G-Wiley/RK05_Emulator_Tester_System_v2/Setting up the emulator.pdf

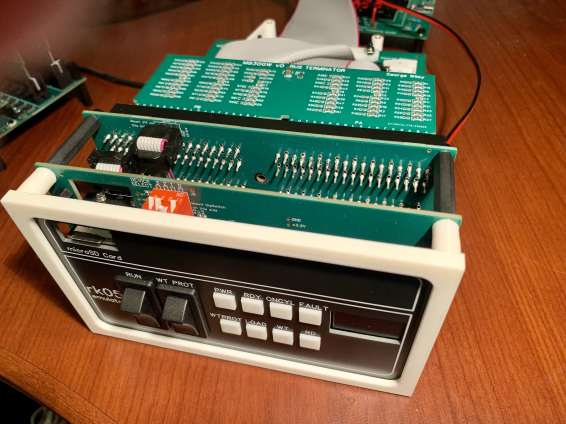
[picture p1: figure]

14-May-2026 | Seng up the emulator v09.docx | Page 1

Connecng the emulator to the Disk Controller:
- The order of the following setup steps isn’t important except to turn the power on as the last step.
- Plug in the terminator board and the “A1” or “A2” RK05 bus interface cable. The two RK05 bus slots on the emulator are electrically the same so either board can go in either slot. The component side faces up. It’s easier to access the Adapter Board when the terminator board is installed in the top slot. It might also be convenient to connect oscilloscope probes to the RK05 bus signals from the top of the M993GW adapter board, and in that case it’s beer to plug the terminator into the boom connector.

There is a keying slot between the two sets of gold contact fingers on both the terminator board and on the cable. There is a guide on the emulator main board silkscreen that shows the proper orientaon of this keying slot.

Silkscreen guide, corresponds to the keying slot

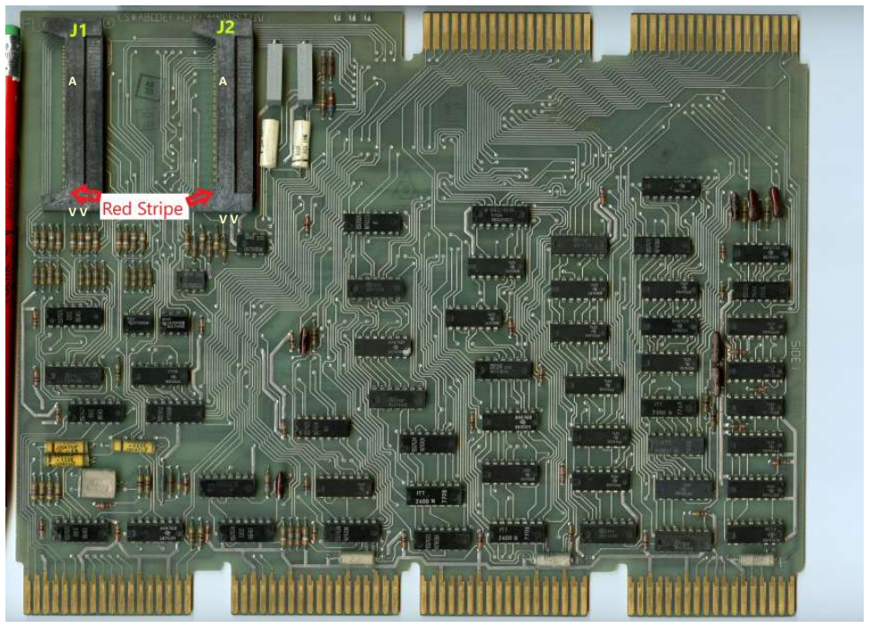
[picture p2: figure]

14-May-2026 | Seng up the emulator v09.docx | Page 2

Connecng to a Disk Controller, PDP-8 Systems
- DEC RK8-E: Connect the unconnected ends of the flat cables from an “A1” RK05-to-RK8-E Cable to the DEC RK8-E M7106 connectors J1 & J2. Connect the flat cable from J1 on the M993GW Adapter Board to J1 on the M7106. Similarly, connect the flat cable from J2 on the M993GW adapter card to J2 on the M7106. It is helpful to use a permanent marker or other means to label the flat cables with “J1” & “J2” so it is clear which cable goes to which connector. If connecng to a DEC RK8-E, then the keying tabs on the flat cable connectors should be sanded off so they will fit into the DEC Berg connectors. A Dremel tool or sharp pair of flush cut diagonal cuers (or both) can also be used to remove the keying tabs. The pin numbering alignment is strange, as shown in the photo: 3M connector pin 1 (red stripe) corresponds to Berg pin VV, and 3M pin 40 corresponds to Berg pin A.

DEC RK8-E

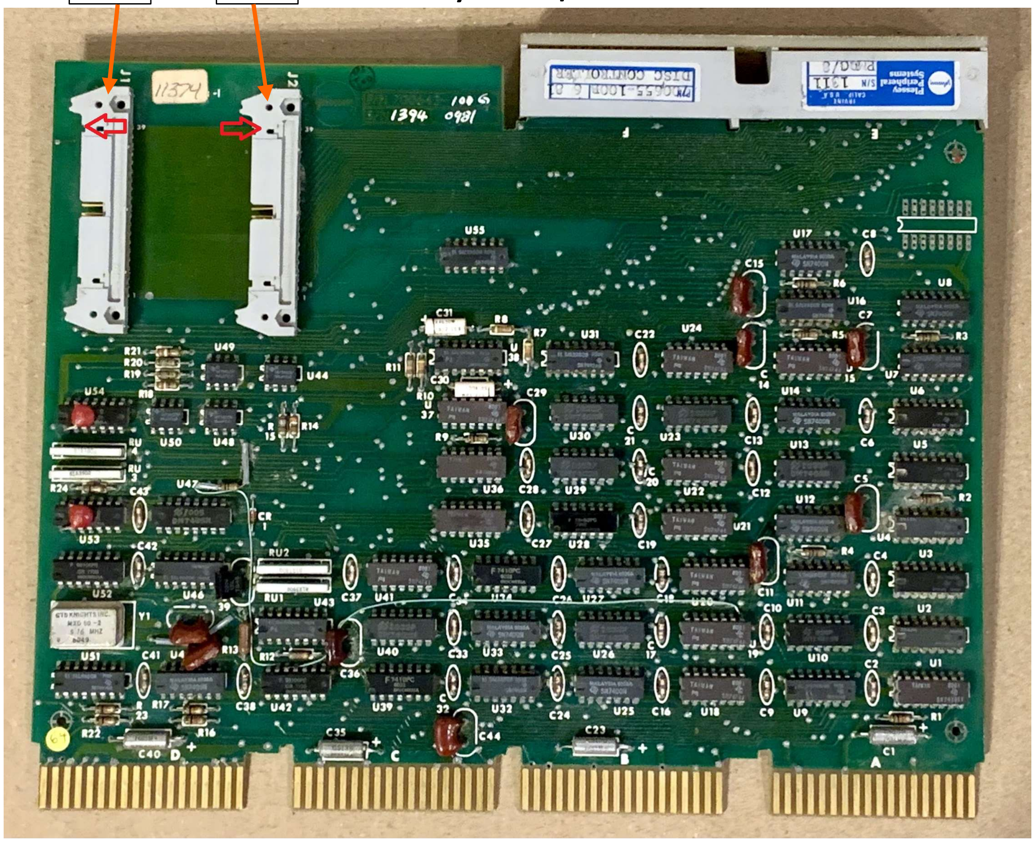
[picture p3: figure]

14-May-2026 | Seng up the emulator v09.docx | Page 3
- The Plessey PM-DC/8 has J1 & J2 clearly labelled on the silkscreen. J1 on the M993GW (emulator accessory A1 or A4) connects to J1 on the PM-DC/8, and J2 on the M993GW connects to J2 on the PM-DC/8. Red arrows in the photo below show the orientaon of the red stripe on the cable. Note that this is the opposite orientaon compared to the DEC RK8-E. The keying slots on the controller board headers are not in the proper orientaon to accept the keying ribs on the cables from the emulator.

The keying tabs on the flat cable connectors should be sanded off so they will fit into the J1 & J2 connectors on the PM-DC/8. If the keying tab is not removed then the flat cable will only fit into J1 & J2 in the wrong direcon and the red stripe on the cables will be oriented incorrectly (at the boom of J1 & J2). A Dremel tool or sharp pair of flush cut diagonal cuers (or both) can also be used to remove the keying tabs. The pin numbering alignment is strange, as shown in the photo: the red stripe on the cable corresponds to J1 & J2 pins 39 & 40, and the side of the cable without the red stripe corresponds to J1 & J2 pins 1 & 2.

Aer plugging in the cables, ensure that the orientaon of the cables and red stripe are correct.

Plessey PM-DC/8

J1 J2

14-May-2026 | Seng up the emulator v09.docx | Page 4
- OS/8 Bootstrap for RK8-E + RK05
Load the following two-word program, run from 0030:

Address Content
0030 6743
0031 5031

How to:
1. Copy the file “os8.rke” or another suitable OS/8 image to a microSD card.
Confirm that no other rke files exist at the root level on the microSD card.

### 2. Remove the microSD card from your computer and insert the card into the slot on the

front of the RK05 emulator.
3. Flip the RUN/LOAD switch on the front of the RK05 emulator to the “RUN” posion.
4. Wait for the microSD card image to load. When that’s complete, the following lights will be illuminated on the front of the emulator: PWR, RDY, ONCYL
5. Perform the following steps via the front panel of the PDP-8.

### 6. Set SR = 0030 7. ADDR LOAD 8. Set SR = 6743 9. DEP 10. Set SR = 5031 11. DEP 12. Set SR = 0030 13. ADDR LOAD 14. CONT

- Conversion to/from emulator rke files and SIMH RK05 PDP-8 images hps://svn.so-much-stuff.com/svn/trunk/pdp8/8tools/ hps://svn.so-much-stuff.com/svn/trunk/pdp8/8tools/doc/
o dsk2rke converts .dsk format to RKE (emulator) format
PERL: hps://svn.so-much-stuff.com/svn/trunk/pdp8/8tools/dsk2rke
doc: hps://svn.so-much-stuff.com/svn/trunk/pdp8/8tools/doc/dsk2rke.md o rke2dsk converts RKE format to .dsk (SIMH) format
PERL: hps://svn.so-much-stuff.com/svn/trunk/pdp8/8tools/rke2dsk
doc: hps://svn.so-much-stuff.com/svn/trunk/pdp8/8tools/doc/rke2dsk.md o rkechk checks an RKE file and a DSK file for equivalence
PERL: hps://svn.so-much-stuff.com/svn/trunk/pdp8/8tools/rkechk
doc: hps://svn.so-much-stuff.com/svn/trunk/pdp8/8tools/doc/rkechk.md

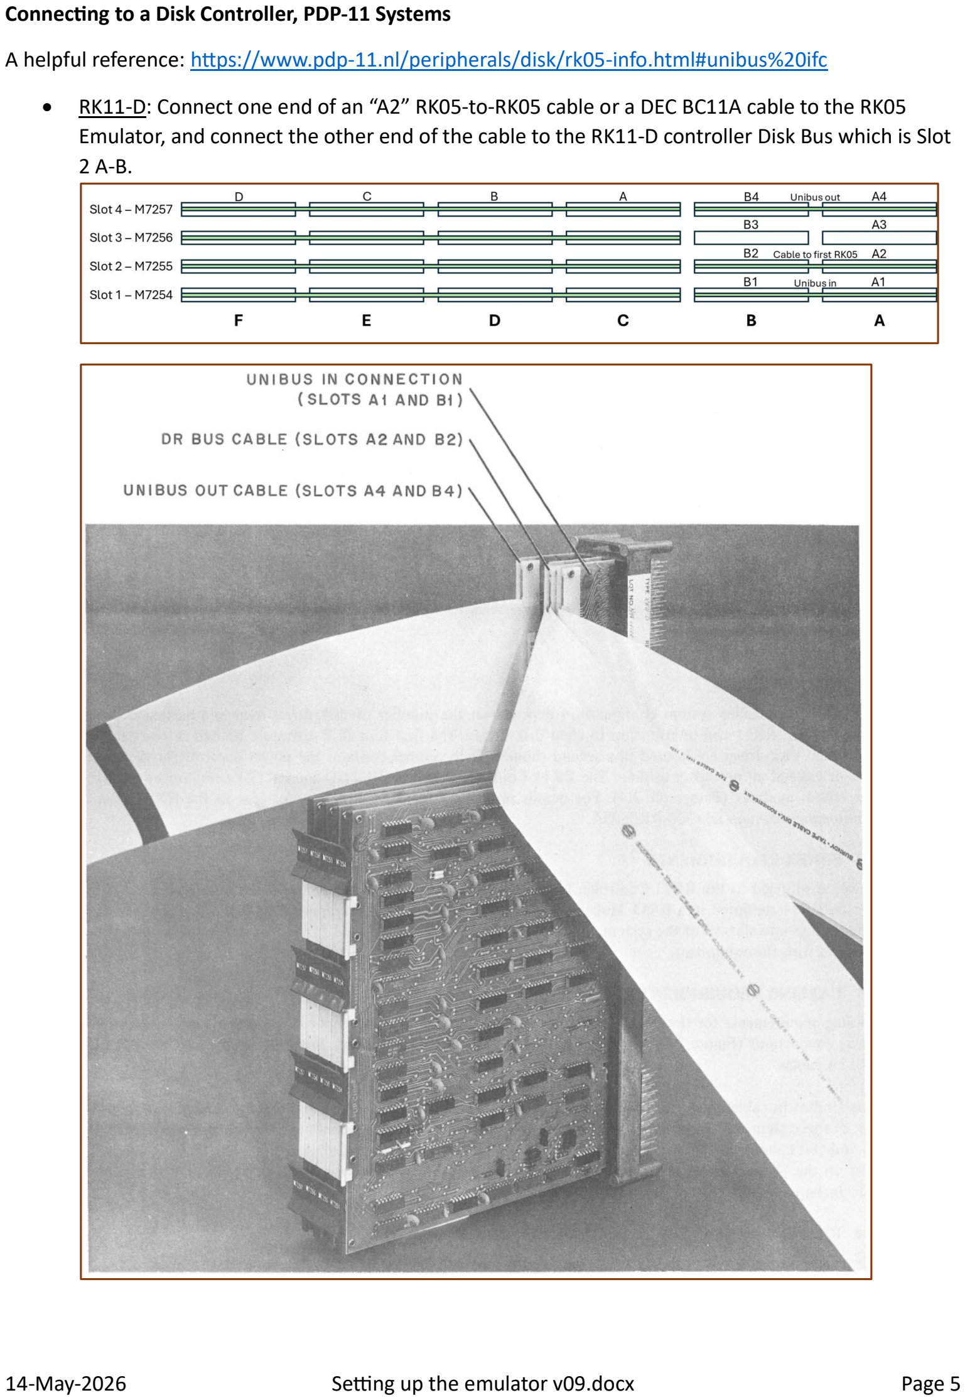
[picture p4: page 5]

14-May-2026 | Seng up the emulator v09.docx | Page 5

Connecng to a Disk Controller, PDP-11 Systems
A helpful reference: hps://www.pdp-11.nl/peripherals/disk/rk05-info.html#unibus%20ifc
- RK11-D: Connect one end of an “A2” RK05-to-RK05 cable or a DEC BC11A cable to the RK05 Emulator, and connect the other end of the cable to the RK11-D controller Disk Bus which is Slot 2 A-B.

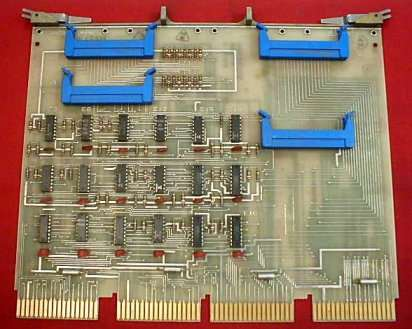
[picture p5: figure]

14-May-2026 | Seng up the emulator v09.docx | Page 6
- RKV11-D: Connect one end of an “A1” RK05-to-RK8-E cable into a slot on the RK05 Emulator. Connect the unconnected ends of the flat cables from the “A1” RK05-to-RK8-E Cable to flat cable connectors on the DEC M7268 board that is part of the RKV11-D controller. It is helpful to use a permanent marker or other means to label the flat cables so it is clear which cable goes to which connector. The keying tabs on the flat cable connectors should be sanded off so they will fit into the DEC Berg connectors. A Dremel tool or sharp pair of flush cut diagonal cuers (or both) can also be used to remove the keying tabs. The pin numbering alignment is strange, as shown in the photo: 3M connector pin 1 (red stripe) corresponds to Berg pin VV, and 3M pin 40 corresponds to Berg pin A.

DEC M7268

Image source: hps://www.pdp-11.nl/peripherals/disk/rk05-info.html#unibus%20ifc

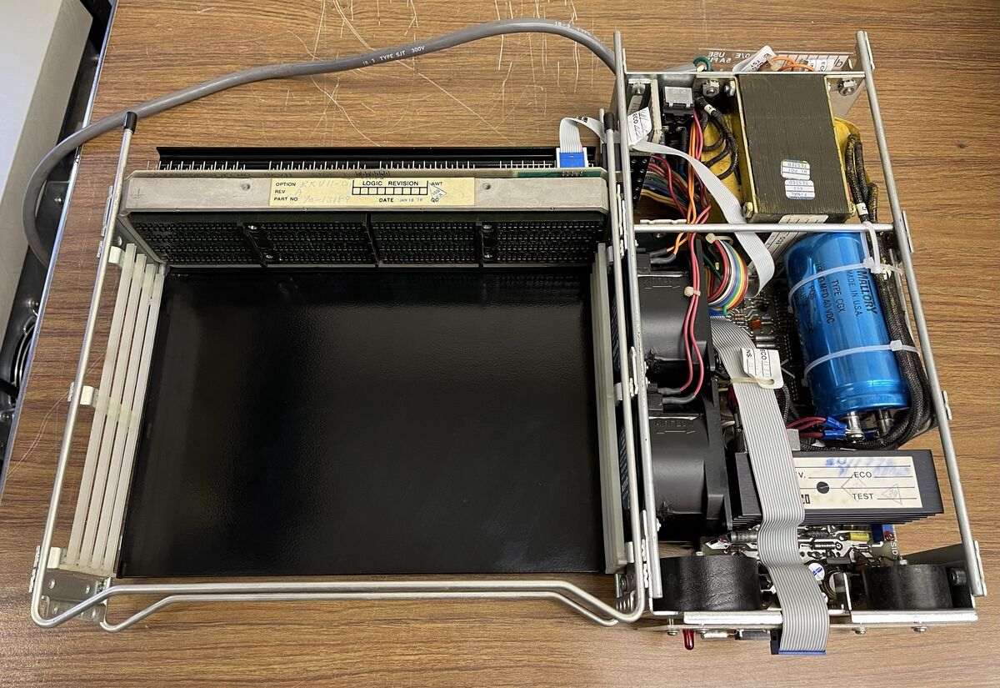
[picture p6: figure]

14-May-2026 | Seng up the emulator v09.docx | Page 7

Image source: hps://gunkies.org/wiki/RK11_disk_controller#RKV11-D

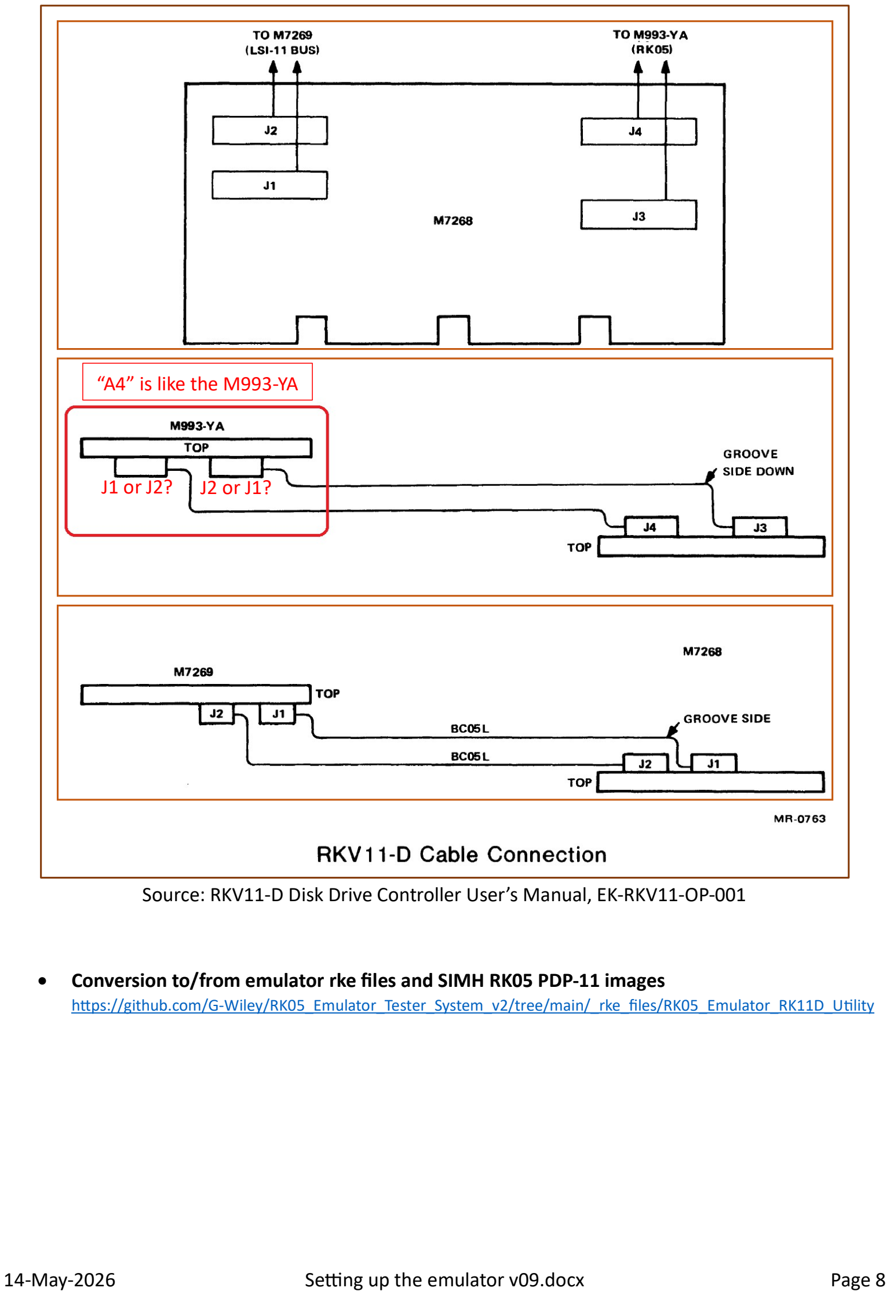
[picture p7: page 8]

14-May-2026 | Seng up the emulator v09.docx | Page 8

Source: RKV11-D Disk Drive Controller User’s Manual, EK-RKV11-OP-001

- Conversion to/from emulator rke files and SIMH RK05 PDP-11 images
hps://github.com/G-Wiley/RK05_Emulator_Tester_System_v2/tree/main/_rke_files/RK05_Emulator_RK11D_Ulity

“A4” is like the M993-YA

J1 or J2? J2 or J1?

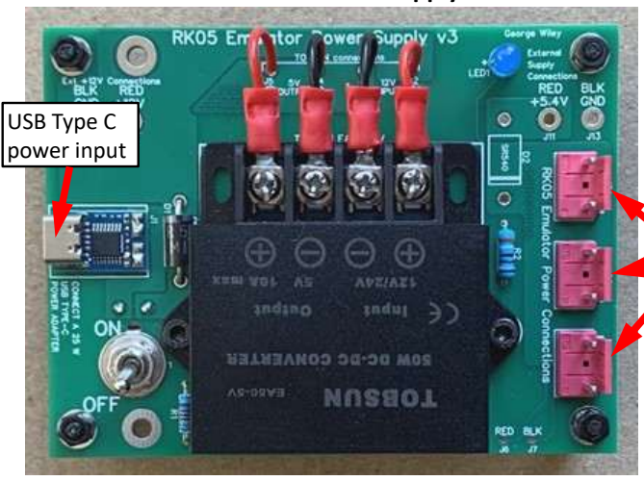
[picture p8: figure]
USB Type C power input

14-May-2026 | Seng up the emulator v09.docx | Page 9

Emulator Power Supply
- Connect one end of the red/black power cable to the power header on the emulator. Connect the other end of the power cable to any one of the three power headers on the Emulator Power Supply. Up to three emulators can be connected to a single Emulator Power Supply.

Emulator Power Supply

- Connect a 25-wa USB Type C power module to the USB Type C connector on the Emulator Power Supply. This Type C power module is included with the “A7” Emulator Power Supply. For example, this is the type of power module shipped with the “A7” kit: hps://www.amazon.com/dp/B097MVXSQ5
Emulator Power Supply versions v2 and above have a power input switch located near the USB connector.

Power
Headers

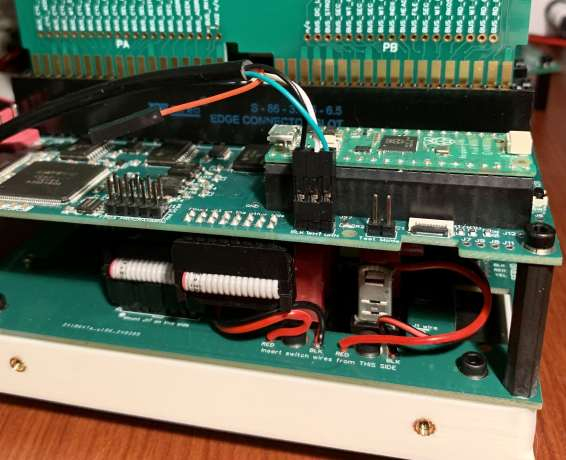
[picture p9: figure]

14-May-2026 | Seng up the emulator v09.docx | Page 10

Connecng a serial console
- If it is necessary to observe the emulator event log data, then connect a USB serial cable to the serial “DEBUG” port, as shown. The black wire is “GND”, white is “TX”, green is “RX”. The red wire on the USB serial cable is unconnected. The silkscreen on the main board indicates which wire color should connect to each of the three pins. Either a 5 volt or 3.3 volt USB serial cable can be used; the emulator has 5 volt tolerant drivers and receivers on the TX and RX signals and is compable with 3.3 volt and 5 volt signal levels. With USB side of the serial cable plugged into in the computer, set your terminal emulator to use whichever COM port is assigned to the cable. Tip: bring up the Windows Device Manager first, then plug the USB cable into the computer to observe which COM port was just assigned when the USB serial cable was inserted. Baud rate is 460,800 bits per second, 8 bits, no parity. The high data rate is used so the serial port can keep up when logging sector reads and writes when the logging mode is selected.
- Set the RUN/LOAD switch on the front panel of the emulator to the “LOAD” posion.
- Plug in the USB Type C charger and turn on the on-board power switch.

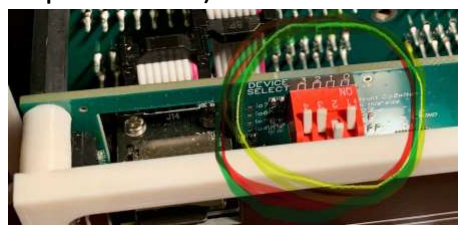
[picture p10: figure]

14-May-2026 | Seng up the emulator v09.docx | Page 11

Using the Emulator:
- Insert a microSD card into the microSD slot accessible through the front panel. The card must have a valid rk05 emulator file with an “rke” file extension at the root level. Example rke files are provided in the emulator repository on github: hps://github.com/G-Wiley/RK05_Emulator_Tester_System_v2/tree/main/_rke_files
The emulator will load the first file it finds that has an rke file extension.
- The Drive Address can be set using the 4-posion dipswitch located behind the front panel. The dipswitch is idenfied as “DEVICE SELECT” on the board silkscreen next to the dipswitch. The individual switches are idenfied as 0 through 3 on the silkscreen. Switches 0 through 2 are a 3-bit binary drive address value. The selected Drive Address immediately appears in the OLED display on the front panel. The Drive Address seng is effecve only when the emulator is in the “LOAD” state.
- The following example shows the switches set to address 2. The switch on the right has binary weight of 2⁰

, the next switch to the le which is in a different state than the other switches is 2¹ ,
the next switch to the le is 2² , and the switch on the far le selects fixed mode (which is not yet implemented).

Although some drives use one-hot individual select enable signals to select the drive, this address switch is always a binary representaon of the drive address. The large digit in the front panel display confirms the address that is selected.
- Aer the RUN/LOAD switch is turned to the RUN posion, the emulator will ignore the state of the dipswitches. Only drive addresses 0 through 3 are valid for PDP-8 RK8-E mode which uses individual select signals on the disk bus. Drive addresses 0-7 can be used in RK11-D/E modes which use a binary-encoded drive address on the disk bus. The disk controller outputs a signal on the disk bus so that drives will use the proper drive-selecon mode for the controller. The RK05 emulator and real RK05 drives respond properly to this signal from the controller, but some other drives (such as Diablo series 30) support only individual select signals. The most significant switch, switch 3, (the switch on the le) enables RK05f mode. RK05f mode is not yet supported; the proper double-address will appear in the display, but the FPGA and soware do not yet support this mode. This is a planned future upgrade.
- Flip the RUN/LOAD switch to the “RUN” posion. The emulator will read the rk05 disk image file from the card and store the data in the emulator’s DRAM. Progress of reading the file will appear in the display. When the enre file has been read, the front panel LEDs will update to indicate RDY and ONCYL.
- To observe a log of RK05 bus events such as Seek, Restore, Read and Write: type “L” on the aached terminal (commands are case insensive). To stop logging type “S”. There is a bug which may cause the emulator to lock up aer receiving 5,000 to 10,000 bus events while logging. This problem does not occur when logging is off.

14-May-2026 | Seng up the emulator v09.docx | Page 12
- To unload and save data from the emulator DRAM back to the microSD card, flip the RUN/LOAD switch back to the LOAD posion. Progress of wring the file will appear in the display. When the enre file has been wrien, the front panel LEDs will update to indicate LOAD.
- If there is an error, then it will show in the emulator front panel display and on the aached terminal and the ERROR indicator on the front panel will flash. The flashing error indicator can be cleared by first holding the WTPROT switch while toggling the state of the RUN/LOAD switch.
