G-Wiley/RK05_Emulator_Tester_System_v2/_rke_files/Sector Timing and Data Diagrams v05.pdf

Bit times from sector pulse to start bit Number of data bits after the start bit Data Block, includes Cylinder Address, data, CRC, etc.

Ideally this is only the data between the Sync Bit and Postamble, but it may contain some of the all-zero Postamble bits

1w 1w | 1 to n 16-bit words
Preamble | S | Cylinder Address, Data, CRC, etc. | Postamble

Disk_Sector_Pulse_L

RK8-E Write_Gate_L

DG Write_Gate_L

Read_Gate_L

DG Erase Zone | Sync Bit | DG Erase Zone
DRAM Internal Sector Block Base+0 | Base+1 | Base+2 | Base+2+n-1
4-February-2025 | Sector Timing and Data Diagrams (doc file v05) | page 1

Bit times from sector pulse to start bit Number of data bits after the start bit Data Block, includes Cylinder Address, data, CRC, etc.

Ideally this is only the data between the Sync Bit and Postamble, but it may contain some of the all-zero Postamble bits

1w 1w

S | Cylinder Address, Data, CRC, etc. | Postamble

Disk_Sector_Pulse_L

Read_Gate_L

Sync Bit

DRAM Internal Sector Block Base+0 | Base+1 | Base+2 | Base+2+n-1
0 Read Base+0 | Read Base+1 Read Data block Base+2 and after

## Sector Read Timing

### 1 to n 16-bit words

0 | 1 | 2 | 3,4 5 | 6 | 7 0
0 | 1 | 2 | 3,4 5 | 6 | 7 0

Preamble

Read_Gate_L

4-February-2025 | page 2

If Read_Gate_L remains active after the last bit of the Data Block has been output, then the emulator will send all-zero data to the controller.

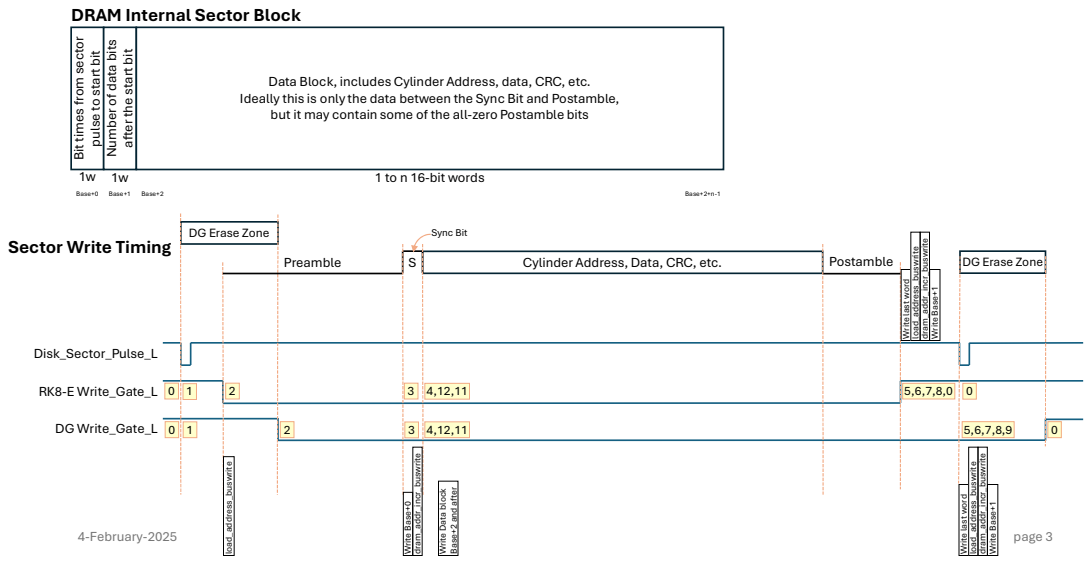
[picture p35: page 3]
Preamble; Cylinder Address, Data, CRC, etc.; Postamble; Disk_Sector_Pulse_L; RK8-E Write_Gate_L; DG Write_Gate_L; DRAM Internal Sector Block Base+0; Base+1; Base+2; Base+2+n-1; 5,6,7,8,0 load_address_buswrite; Write Base+0 dram_addr_incr_buswrite; Write Data block Base+2 and after; 5,6,7,8,9 Write last word load_address_buswrite; Write Base+1; 4-February-2025; page 3

Bit times from sector pulse to start bit Number of data bits after the start bit Data Block, includes Cylinder Address, data, CRC, etc.

Ideally this is only the data between the Sync Bit and Postamble,
but it may contain some of the all-zero Postamble bits

1 to n 16-bit words

DG Erase Zone

Sector Write Timing

Sync Bit
0 dram_addr_incr_buswrite Write last word load_address_buswrite dram_addr_incr_buswrite Write Base+1

Disk_Sector_Pulse_L

Sync Bit

Preamble + Gap = 8+120+82 = 210 1 | Header + Data + CRC = 16 + 3072 + 16 = 3104 | Postamble = 36

16-sector 1.44 Mbps, 2500 µs = 3600 bits (3571 emulator bits), 1 revolution = 40 ms

210 + 1 + 3104 + 36 = 3351 bits

## RK8-E

Disk_Sector_Pulse_L

Sync Bit

Preamble + Gap = 8+128+80 = 216 1 | Header + Data + Checksum = 16 + 4096 + 16 = 4128 | Postamble = 16

12-sector 1.44 Mbps, 3333.33 µs = 4800 bits (4761 emulator bits), 1 revolution = 40 ms

216 + 1 + 4128+ 16 = 4361 bits

## RK11-D

Margin = 400 bits

Margin = 220 bits

Disk_Sector_Pulse_L

Sync Bit

Preamble + Gap = 9+128+80 = 217 1 | Header + Data + Checksum = 16 + 4608 + 16 = 4640 | Postamble = 16

12-sector 1.545 Mbps, 3333.33 µs = 5150 bits (5128 emulator bits), 1 revolution = 40 ms

217 + 1 + 4640+ 16 = 4874 bits

## RK11-E

Margin = 254 bits

4-February-2025 | Sector Timing and Data Diagrams (doc file v05) | page 4

Disk_Sector_Pulse_L

Sync Bit

Preamble + Gap = 9+201 = 210 1 Header + Label + Data + CRC = 32 + 128 + 4096 + 16 = 4272 Postamble = 16

12-sector 1.6 Mbps, 3333.33 µs = 5333 bits (5333 emulator bits), 1 revolution = 40 ms

210 + 1 + 4272 + 16 = 4499 bits

## Xerox Alto

Disk_Sector_Pulse_L

Sync Bit

Preamble + Gap = 8+187+101 = 296 1 | Header + Data + CRC = 4182 | Postamble = 72

12-sector 1.44 Mbps, 3333.33 µs = 4800 bits (4761 emulator bits), 1 revolution = 40 ms

296 + 1 + 4182+ 72 = 4551 bits

## Data General

Margin = 210 bits

Margin = 834 bits

Disk_Sector_Pulse_L

Sync Bit

Preamble + Gap = 239 bits | 1 | Header + Data + CRC = 16 + 2048 + 16 = 2080 bits | Postamble = 16

24-sector 2.50 Mbps, 1041.67 µs = 2604 bits (2604 emulator bits), 1 revolution = 25 ms

239 + 1 + 2080 + 16 = 2336 bits

HP2100, 13210A

Margin = 268 bits

4-February-2025 | Sector Timing and Data Diagrams (doc file v05) | page 5

Disk_Sector_Pulse_L

Sync Bit

Preamble + Gap = 210 | 1 | Header + Data + CRC = 16 + 3072 + 16 = 3104 | Postamble = 16

16-sector 1.44 Mbps, 2500 µs = 3600 bits (3571 emulator bits), 1 revolution = 40 ms

210 + 1 + 3104 + 36 = 3351 bits

### 16 Sector 1.44 Mbps

Disk_Sector_Pulse_L

Sync Bit

Preamble + Gap = 210 | 1 | Header + Data + CRC = 16 + 4096 + 16 = 4128 | Postamble = 16

12-sector 1.44 Mbps, 3333.33 µs = 4800 bits (4761 emulator bits), 1 revolution = 40 ms

210 + 1 + 4128+ 16 = 4355 bits

### 12 Sector 1.44 Mbps

Margin = 406 bits

Margin = 220 bits

Disk_Sector_Pulse_L

Sync Bit

Preamble + Gap = 210 | 1 | Header + Data + CRC = 4932 | Postamble = 16

10-sector 1.44 Mbps, 4000 µs = 5760 bits (5714 emulator bits), 1 revolution = 40 ms

210 + 1 + 4932 + 16 = 5159 bits

### 10 Sector 1.44 Mbps

Margin = 555 bits

4-February-2025 | Sector Timing and Data Diagrams (doc file v05) | page 6

Disk_Sector_Pulse_L

Sync Bit

Preamble + Gap = 210 | 1 | Header + Data + CRC = 16 + 6200 + 16 = 6232 | Postamble = 16

8-sector, 5000 µs = 7200 bits (7142 emulator bits), 1 revolution = 40 ms

210 + 1 + 6232 + 16 = 6459 bits

### 8 Sector 1.44 Mbps

Disk_Sector_Pulse_L

Sync Bit

Preamble + Gap = 210 | 1 | Header + Data + CRC 16 + 8000 + 16 = 8032 | Postamble = 16

6-sector, 6666.67 µs = 9600 bits (9523 emulator bits), 1 revolution = 40 ms

210 + 1 + 8032 + 16 = 8259 bits

### 6 Sector 1.44 Mbps

Margin = 1264 bits

Margin = 683 bits

Disk_Sector_Pulse_L

Sync Bit

Preamble + Gap = 210 | 1 | Header + Data + CRC 16 + 13,000 + 16 = 13,032 | Postamble = 16

4-sector, 10,000 µs = 14,400 bits (14,285 emulator bits), 1 revolution = 40 ms

210 + 1 + 13,032+ 16 = 13,259 bits

### 4 Sector 1.44 Mbps

Margin = 1026 bits

4-February-2025 | Sector Timing and Data Diagrams (doc file v05) | page 7
