G-Wiley/RK05_Emulator_Tester_System_v2/PCB_files/103_RK05_Emulator_Dress_Panel/RK05_Emulator_Dress_Panel_v3_ordering_instructions.pdf

RK05_Emulator_Dress_Panel_v3_ordering_instructions_v01.docx | page 1

103 RK05 Emulator Dress Panel v3 ordering instructions
The following instructions serve as a guide to order RK05 Emulator Dress Panel printed circuit boards directly from JLCPCB.
This board has no components and doesn’t require any assembly.
JLCPCB ordering options that are dierent from the default options:
- Click “Add gerber file” and upload the Gerber file: “Gerber_PCB_RK05-Emulator-Dress-Panel-v3_2024-05-07.zip”
- PCB Qty: select the desired quantity
- PCB Color: Black
- Surface Finish: LeadFree HASL
- Remove Order Number: Specify a location
- Click “SAVE TO CART”
- Click "View Cart”
- Click the checkbox on the left side to select the item.
- Click "Secure Checkout” and enter the requested information. Choose the Shipping Method that best suits your delivery time and cost goals.

Note: regarding the “Remove Order Number” option, if “Specify a location” is chosen, then JLCPCB will place the order number in a location that is already specified in the Gerber file. There is no extra charge for selecting this option.
