G-Wiley/RK05_Emulator_Tester_System_v2/PCB_files/105_M993GW_RK05_Adapter_Board/M993GW_Adapter_Board_v3_ordering_instructions.pdf

M993GW_Adapter_Board_v3_ordering_instructions_v01.docx | page 1

A4 M993GW Adapter Board v3 ordering instructions
The following instructions serve as a guide to order M993GW Adapter Board printed circuit boards directly from JLCPCB.
Since building this board requires soldering only a small number of through-hole parts and some minor mechanical assembly, there is no need to have JLCPCB perform any of the assembly.
JLCPCB ordering options that are dierent from the default options:
- Click “Add gerber file” and upload the Gerber file: “Gerber_PCB_M993GW-v3_2024-09-05.zip”
- PCB Qty: select the desired quantity
- Surface Finish: ENIG
- Gold Fingers: Yes
- Chamfered: 30°
- Click “SAVE TO CART”
- Click "View Cart”
- Click "Secure Checkout” and enter the requested information. Choose the Shipping Method that best suits your delivery time and cost goals.
