G-Wiley/RK05_Emulator_Tester_System_v2/PCB_files/107_Emulator_Power_Supply_Board/RK05_Emulator_Power_Supply_Board_v3_ordering_instructions.pdf

RK05_Emulator_Power_Supply_Board_v3_ordering_instructions_v01.docx | page 1

107 RK05 Tester Power Supply Board v3 ordering instructions
The following instructions serve as a guide to order RK05 Tester Power Supply Board printed circuit boards directly from JLCPCB.
Since building this board requires soldering only a small number of through-hole parts and some minor mechanical assembly, there is no need to have JLCPCB perform any of the assembly.
JLCPCB ordering options that are dierent from the default options:
- Click “Add gerber file” and upload the Gerber file:
“Gerber_PCB_RK05-Emulator-Power-Supply-v3 _2024-07-15.zip”
- PCB Qty: select the desired quantity
- Surface Finish: LeadFree HASL
- Mark on PCB: Order Number (Specify Position)
- Click “SAVE TO CART”
- Click "View Cart”
- Click the check box on the left side to select the board
- Click "Secure Checkout” and enter the requested information. Choose the Shipping Method that best suits your delivery time and cost goals.

Note: regarding the “Mark on PCB” option, if “Order Number (Specify Position)” is chosen, then JLCPCB will place the order number in a location that is already specified in the Gerber file. There is no extra charge for selecting this option. The Gerber file specifies the order number to be on the back side of the PCB so it’s not visible when the board is oriented top-side-up, but you must select this option so that JLCPCB follows what is specified in the Gerber file.
