G-Wiley/RK05_Emulator_Tester_System_v2/Diablo_Adapters/Adapter_P_Keystone_v2/ordering_instructions_Diablo_Adapter_P_Keystone_v2_PCB.pdf

ordering_instructions_Diablo_Adapter_P_Keystone_v2_PCB.docx | page 1

Diablo Adapter P Keystone Board v2 PCB ordering instructions (no SMT assembly needed)
The following instructions serve as a guide to order Diablo Adapter P Keystone PCBs directly from JLCPCB Check the JLCPCB website to see if there are any coupons that might relate to your order.
Under the “1 – 4 Layers” category, click the “Quote Now” button.
JLCPCB ordering options that are dierent from the default options:
- Upload the Gerber file: “Gerber_PCB_RK05-Diablo-Adapter-P-Keystone-v2_2025-01-13.zip”
- PCB Qty: select the desired quantity
- Surface Finish: LeadFree HASL
- Mark on PCB: Order Number(Specify Position)
(Note that the position of the order number is already specified in the Gerber file. All you need to do is to select this option.)
- Click “SAVE TO CART”
- View the cart and proceed through the checkout process. Don’t forget to select (check) the items in the cart that you would like to order. Choose the shipping method based on which price and delivery time suits your needs.
