G-Wiley/RK05_Emulator_Tester_System_v2/Source_Code/Pico_SW_Tester/RK05_Tester_v01x19/Debugging Tester v01x19.docx

Debugging v01x19

Updates:

- ✓

List of items to fix, Starting 21-Sep-2025:

- Display an error if index pulse is missing
- Display an error if sector pulse is missing
