G-Wiley/RK05_Emulator_Tester_System_v2/design_notes/RK05 emulator v2 block diagram v00.pdf

# RK05 emulator v2 Block Diagram

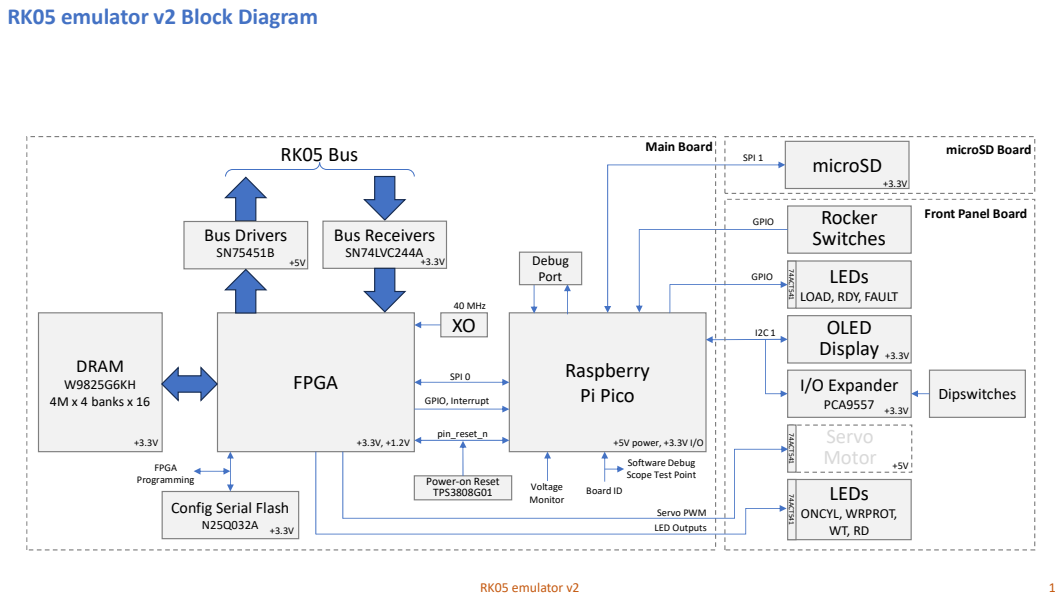
[picture p113: page 1]
FPGA; SPI 0; RK05 emulator v2; Raspberry Pi Pico; LEDs LOAD, RDY, FAULT; LEDs ONCYL, WRPROT, WT, RD; microSD SPI 1; GPIO; OLED Display; I/O Expander; PCA9557; Dipswitches ⁷⁴ACT541 74ACT541; Rocker Switches; Servo Motor ⁷⁴ACT541; GPIO, Interrupt; Config Serial Flash N25Q032A; 40 MHz; Bus Receivers SN74LVC244A; Bus Drivers SN75451B; RK05 Bus; DRAM W9825G6KH 4M x 4 banks x 16; pin_reset_n; Main Board; microSD Board; FPGA Programming; Servo PWM LED Outputs; Debug Port; Voltage Monitor; Board ID

Front Panel Board

+5V power, +3.3V I/O
Software Debug
Scope Test Point

Power-on Reset
TPS3808G01
