G-Wiley/RK05_Emulator_Tester_System_v2/Source_Code/Pico_SW_Emulator/RK05_Emulator_v02x07/emulator_microsd_actuator.h

// *********************************************************************************
// emulator_microsd_actuator.h
//  definitions and functions related to the emulator microSD card actuator
//  to open and close the drive door
// *********************************************************************************
// This file is not used yet, maybe this will be included in the emulator_hardware.cpp module

void close_drive_door();
void open_drive_door();
