G-Wiley/RK05_Emulator_Tester_System_v2/Source_Code/Pico_SW_Emulator/RK05_Emulator_v02x07/emulator_state.h

// *********************************************************************************
// emulator_state.h
//  definitions and functions related to the RUN/LOAD emulator state
// 
// *********************************************************************************
// 
//#include "disk_state_definitions.h"

void process_run_load_state (struct Disk_State *dstate);
