G-Wiley/RK05_Emulator_Tester_System_v2/Source_Code/Pico_SW_Emulator/RK05_Emulator_v02x07/emulator_command.h

// *********************************************************************************
// emulator_command.h
//  definitions and functions related to parsing and execution of emulator 
//  Interface Test Mode commands
// 
// *********************************************************************************
// 

void command_parse_and_dispatch (Disk_State* dstate);
int extract_command_fields(char* line_ptr);
void emulator_command_mode(Disk_State* dstate);
