G-Wiley/RK05_Emulator_Tester_System_v2/Source_Code/Pico_SW_Tester/RK05_Tester_v01x19/dpd_definitions.h

// *********************************************************************************
// dpd_definitions.h
//   header for Disk Parameter Description definitions
// *********************************************************************************
// 

#define DPDmagicLength 10
#define DPDversionLength 4

#define MaxBitRate 20000000
#define MinBitRate  1000000
#define MaxNumberOfCylinders 203
#define MinNumberOfCylinders   1
#define MaxNumberOfSectorsPerTrack 4
#define MinNumberOfSectorsPerTrack 32
#define MaxNumberOfHeads 2
#define MinNumberOfHeads 1
#define MaxMicrosecondsPerSector 80000
#define MinMicrosecondsPerSector   600
#define MaxPreamble1Length 99999999
#define MinPreamble1Length 1
#define MaxPreamble2Length 99999999
#define MinPreamble2Length 1
#define MaxPostambleLength 99999999
#define MinPostambleLength 1
#define MaxBitTimesSectorToStart 99999999
#define MinBitTimesSectorToStart 1
#define MaxBitTimesDataBitsAfterStart 99999999
#define MinBitTimesDataBitsAfterStart 1
