G-Wiley/RK05_Emulator_Tester_System_v2/Source_Code/Pico_SW_Tester/RK05_Tester_v01x19/display_state_definition.h

// *********************************************************************************
// display_state_definition.h
//  definitions of the display state
// 
// *********************************************************************************
// 
struct Display_State
{public:
    int display_message_timer;
    int display_invert_timer;
};
