G-Wiley/RK05_Emulator_Tester_System_v2/Source_Code/Pico_SW_Tester/RK05_Tester_v01x19/display_timers.h

// *********************************************************************************
// display_functions.h
//   header for display operations
// *********************************************************************************
// 

#define DISPLAY_INVERT_TIME 3000
