G-Wiley/RK05_Emulator_Tester_System_v2/Source_Code/Pico_SW_Tester/RK05_Tester_v01x19/tester_command.h

// *********************************************************************************
// tester_command.h
//  definitions and functions related to parsing and execution of tester commands
// 
// *********************************************************************************
// 

void command_parse_and_dispatch (Disk_State* dstate);
int extract_command_fields(char* line_ptr);
